mwuerms/rollin/sw/rollingL412/Core/Inc/main.h

#define USR_BTN_Pin LL_GPIO_PIN_13
#define USR_BTN_GPIO_Port GPIOC
#define DBG_TX_Pin LL_GPIO_PIN_2
#define DBG_TX_GPIO_Port GPIOA
#define DBG_RX_Pin LL_GPIO_PIN_3
#define DBG_RX_GPIO_Port GPIOA
#define SPI1_NSS_Pin LL_GPIO_PIN_4
#define SPI1_NSS_GPIO_Port GPIOA
#define USR_LED_Pin LL_GPIO_PIN_13
#define USR_LED_GPIO_Port GPIOB
#define NVIC_PRIORITYGROUP_0         ((uint32_t)0x00000007) /*!< 0 bit  for pre-emption priority,
#define NVIC_PRIORITYGROUP_1         ((uint32_t)0x00000006) /*!< 1 bit  for pre-emption priority,
#define NVIC_PRIORITYGROUP_2         ((uint32_t)0x00000005) /*!< 2 bits for pre-emption priority,
#define NVIC_PRIORITYGROUP_3         ((uint32_t)0x00000004) /*!< 3 bits for pre-emption priority,
#define NVIC_PRIORITYGROUP_4         ((uint32_t)0x00000003) /*!< 4 bits for pre-emption priority,
