mwuerms/rollin/sw/avrgcc/r1/pid.h

/**
 * Martin Egli
 * 2022-09-21
 *
 * pid controller module
 */

#ifndef _PID_H_
#define _PID_H_

// - include -------------------------------------------------------------------
#include <stdint.h>

// - public functions ----------------------------------------------------------

void pid_init(float kp, float ki, float kd);
float pid_exec(float error, float delta_t);

#endif // _PID_H_
