mwuerms/rollin/sw/rollin2/Core/Inc/project.h

/*
 * Martin Egli
 * 2025-07-02
 * project definitions and includes
 */

#ifndef INC_PROJECT_H_
#define INC_PROJECT_H_

#include <stdint.h>
#include <stdbool.h>
#include <stddef.h>
#include "main.h"

/* template to use later on
uint32_t primask;

primask = __get_PRIMASK();  // Save current interrupt state
__disable_irq();            // Disable all interrupts

// --- Critical Section Start ---
/ * Your critical code here * /
// --- Critical Section End ---

__set_PRIMASK(primask);     // Restore previous interrupt state
*/


#endif // INC_PROJECT_H_
