mwuerms/rollin/sw/avrgcc/r1/project.h

/**
 * Martin Egli
 * 2021-09-16
 *
 * basic project definitions
 */

#ifndef _PROJECT_H_
#define _PROJECT_H_
/* - includes --------------------------------------------------------------- */
#include <stdint.h>
#include "macrolib.h"

// - public definitions --------------------------------------------------------
#define RET_OK (0)
#define RET_ERR (1)

#define RET_AGAIN (RET_OK)
#define RET_STOP (RET_ERR)

/* - public variables ------------------------------------------------------- */
extern volatile uint8_t global_events;
#define EV_WAKEUP _BV(0)
#define EV_UPDATE_PWM _BV(1)
#define EV_READ_SENSOR _BV(2)

#define SEND_EVENT(ev) global_events |= ev

/* - functions -------------------------------------------------------------- */

#endif /* _PROJECT_H_ */
