mwuerms/rollin/sw/test1/Core/Src/main.c

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
/* Includes ------------------------------------------------------------------*/
#include "main.h"
#include "usb_device.h"

SPI_HandleTypeDef hspi1;

TIM_HandleTypeDef htim1;
TIM_HandleTypeDef htim2;

void SystemClock_Config(void);
static void MX_GPIO_Init(void);
static void MX_TIM1_Init(void);
static void MX_TIM2_Init(void);
static void MX_SPI1_Init(void);
/* USER CODE BEGIN 0 */
static volatile uint16_t sine_lookup_table[] = {32767, 37043, 41247, 45306, 49150, 52714, 55936, 58762, 61144, 63039, 64417, 65253, 65534, 65253, 64417, 63039, 61144, 58762, 55936, 52714, 49150, 45306, 41247, 37043, 32767, 28490, 24286, 20227, 16383, 12819, 9597, 6771, 4389, 2494, 1116, 280, 0, 280, 1116, 2494, 4389, 6771, 9597, 12819, 16383, 20227, 24286, 28490};
static const volatile uint16_t sine_lookup_table_size = sizeof(sine_lookup_table)/sizeof(sine_lookup_table[0]);
static volatile uint16_t pwm_A_index, pwm_B_index, pwm_C_index;
static uint16_t _inc(uint16_t x, uint16_t max) {
	if(x < max) {
		return x+1;
	}
	return 0;
}
void HAL_TIM_PWM_PulseFinishedCallback(TIM_HandleTypeDef *htim) {
	if(htim == &htim1) {
		HAL_GPIO_WritePin(GPIOA, GPIO_PIN_15, GPIO_PIN_SET);
		if(htim->Channel == HAL_TIM_ACTIVE_CHANNEL_1) {
			HAL_GPIO_WritePin(GPIOA, GPIO_PIN_15, GPIO_PIN_RESET);
			HAL_GPIO_WritePin(GPIOA, GPIO_PIN_15, GPIO_PIN_SET);
			pwm_A_index = _inc(pwm_A_index, sine_lookup_table_size-1);
			TIM1->CCR1 = sine_lookup_table[pwm_A_index];
		}
		if(htim->Channel == HAL_TIM_ACTIVE_CHANNEL_2) {
			HAL_GPIO_WritePin(GPIOA, GPIO_PIN_15, GPIO_PIN_RESET);
			HAL_GPIO_WritePin(GPIOA, GPIO_PIN_15, GPIO_PIN_SET);
			HAL_GPIO_WritePin(GPIOA, GPIO_PIN_15, GPIO_PIN_RESET);
			HAL_GPIO_WritePin(GPIOA, GPIO_PIN_15, GPIO_PIN_SET);
			pwm_B_index = _inc(pwm_B_index, sine_lookup_table_size-1);
			TIM1->CCR2 = sine_lookup_table[pwm_B_index];
		}
		if(htim->Channel == HAL_TIM_ACTIVE_CHANNEL_3) {
			HAL_GPIO_WritePin(GPIOA, GPIO_PIN_15, GPIO_PIN_RESET);
			HAL_GPIO_WritePin(GPIOA, GPIO_PIN_15, GPIO_PIN_SET);
			HAL_GPIO_WritePin(GPIOA, GPIO_PIN_15, GPIO_PIN_RESET);
			HAL_GPIO_WritePin(GPIOA, GPIO_PIN_15, GPIO_PIN_SET);
			HAL_GPIO_WritePin(GPIOA, GPIO_PIN_15, GPIO_PIN_RESET);
			HAL_GPIO_WritePin(GPIOA, GPIO_PIN_15, GPIO_PIN_SET);
			pwm_C_index = _inc(pwm_C_index, sine_lookup_table_size-1);
			TIM1->CCR3 = sine_lookup_table[pwm_C_index];
		}
		HAL_GPIO_WritePin(GPIOA, GPIO_PIN_15, GPIO_PIN_RESET);
	}
}

void HAL_GPIO_EXTI_Callback(uint16_t GPIO_Pin) {
	asm("NOP");
}

#define COM_BUFFER_SIZE	(256)
static struct {
	uint8_t data[COM_BUFFER_SIZE];
	uint16_t wr_idx;
} com_buffer;

void com_clear_buffer(void) {
	com_buffer.wr_idx = 0;
}

#include "usbd_cdc_if.h"
void com_send_buffer(void) {
	if(com_buffer.wr_idx == 0) {
		// nothing to send
		return;
	}
	if(CDC_Transmit_FS(com_buffer.data, com_buffer.wr_idx) == 0) {
		// OK
		asm("NOP");
	}
}


uint32_t com_append_char(char c) {
	if(com_buffer.wr_idx < (COM_BUFFER_SIZE-2)) {
		com_buffer.data[com_buffer.wr_idx++] = c;
		return 1;
	}
	return 0;
}

void com_append_string(char *str) {
	char c;
	// copy string
	while(1) {
		c = *str++;
		if(c == '\0') {
			// found end, do not copy
			break;
		}
		if(com_append_char(c) == 0) {
			// buffer full, stop
			break;
		}
	}
}

void com_append_int16(int16_t value) {
	uint16_t digit_pos, use_char;
	int16_t digits[] = {10000, 1000, 100, 10, 1};
	uint8_t digit_value;
	use_char = 0;
	// sign
	if(value < 0) {
		value *= -1;
		if(com_append_char('-') == 0) {
			// buffer full, stop
			return;
		}
	}
	if(value == 0) {
		// only append '0', and done here
		com_append_char('0');
		return;
	}
	for(digit_pos = 0; digit_pos < (sizeof(digits)/sizeof(digits[0])); digit_pos++) {
		digit_value = (uint8_t)(value/digits[digit_pos]);
		if((digit_value != 0) || (use_char != 0)) {
			use_char = 1;
			if(com_append_char('0'+digit_value) == 0) {
				// buffer full, stop
				return;
			}
			value -= digit_value * digits[digit_pos];
		}
	}
}

void com_append_int32(int32_t value) {
	uint16_t digit_pos, use_char;
	int32_t digits[] = {1000000000, 100000000, 10000000, 1000000, 100000, 10000, 1000, 100, 10, 1};
	uint8_t digit_value;
	use_char = 0;
	// sign
	if(value < 0) {
		value *= -1;
		if(com_append_char('-') == 0) {
			// buffer full, stop
			return;
		}
	}
	if(value == 0) {
		// only append '0', and done here
		com_append_char('0');
		return;
	}
	for(digit_pos = 0; digit_pos < (sizeof(digits)/sizeof(digits[0])); digit_pos++) {
		digit_value = (uint8_t)(value/digits[digit_pos]);
		if((digit_value != 0) || (use_char != 0)) {
			use_char = 1;
			if(com_append_char('0'+digit_value) == 0) {
				// buffer full, stop
				return;
			}
			value -= digit_value * digits[digit_pos];
		}
	}
}

void com_append_float(float f, uint32_t nb_dec_places) {
	int32_t x;

	x = (int32_t)f;
	com_append_int32(x);

	if(nb_dec_places == 0) {
		// do not add any decimal places
		return;

	}
	if(nb_dec_places >= 9) {
		// max is 9
		nb_dec_places = 9;
	}

	f -= (float)x;
	if(f < 0.0f) {
		f *= -1;
	}
	com_append_char('.');
	// eval nb leading '0' of part after '.'
	for(uint16_t n = 0; n < nb_dec_places; n++) {
		f *= 10;
		x = (uint8_t)f;
		f -= (float)x;
		com_append_char('0'+x);
	}
}

void _wait_some_time(void) {
		asm("NOP");
	for(uint32_t cnt = 100000; cnt; cnt--) {
	}
}

#define READ_CMD  (0x80)
#define WRITE_CMD (0x00)
void mpu9250_read_who_am_i(void) {
  uint8_t tx_data[1+1] = {READ_CMD|117};
  uint8_t rx_data[sizeof(tx_data)];
  HAL_GPIO_WritePin(SPI1_NSS_GPIO_Port, SPI1_NSS_Pin, GPIO_PIN_RESET);
  HAL_SPI_TransmitReceive(&hspi1, tx_data, rx_data, sizeof(tx_data), 10000);
  HAL_GPIO_WritePin(SPI1_NSS_GPIO_Port, SPI1_NSS_Pin, GPIO_PIN_SET);
}

void mpu9250_read_config(void) {
  uint8_t tx_data[1+7] = {READ_CMD|26};
  uint8_t rx_data[sizeof(tx_data)];
  HAL_GPIO_WritePin(SPI1_NSS_GPIO_Port, SPI1_NSS_Pin, GPIO_PIN_RESET);
  HAL_SPI_TransmitReceive(&hspi1, tx_data, rx_data, sizeof(tx_data), 10000);
  HAL_GPIO_WritePin(SPI1_NSS_GPIO_Port, SPI1_NSS_Pin, GPIO_PIN_SET);
}

void mpu9250_write_config(void) {
  uint8_t tx_data[] = {WRITE_CMD|26, 0x00, 0x00, (0x03<<2), 0x00, 0x00, 0x00};
  uint8_t rx_data[sizeof(tx_data)];
  HAL_GPIO_WritePin(SPI1_NSS_GPIO_Port, SPI1_NSS_Pin, GPIO_PIN_RESET);
  HAL_SPI_TransmitReceive(&hspi1, tx_data, rx_data, sizeof(tx_data), 10000);
  HAL_GPIO_WritePin(SPI1_NSS_GPIO_Port, SPI1_NSS_Pin, GPIO_PIN_SET);
}

void mpu9250_read_int_config(void) {
  uint8_t tx_data[1+4] = {READ_CMD|55};
  uint8_t rx_data[sizeof(tx_data)];
  HAL_GPIO_WritePin(SPI1_NSS_GPIO_Port, SPI1_NSS_Pin, GPIO_PIN_RESET);
  HAL_SPI_TransmitReceive(&hspi1, tx_data, rx_data, sizeof(tx_data), 10000);
  HAL_GPIO_WritePin(SPI1_NSS_GPIO_Port, SPI1_NSS_Pin, GPIO_PIN_SET);
}

void mpu9250_write_int_config(void) {
  uint8_t tx_data[] = {WRITE_CMD|55, 0xF0, 0x00, 0x00, 0x00};
  uint8_t rx_data[sizeof(tx_data)];
  HAL_GPIO_WritePin(SPI1_NSS_GPIO_Port, SPI1_NSS_Pin, GPIO_PIN_RESET);
  HAL_SPI_TransmitReceive(&hspi1, tx_data, rx_data, sizeof(tx_data), 10000);
  HAL_GPIO_WritePin(SPI1_NSS_GPIO_Port, SPI1_NSS_Pin, GPIO_PIN_SET);
}

uint16_t mpu9250_read_sensor_data(uint8_t *rx_data) {
  uint8_t tx_data[1+3*2+1*2+3*2] = {READ_CMD|59};
  //uint8_t rx_data[sizeof(tx_data)];
  HAL_GPIO_WritePin(SPI1_NSS_GPIO_Port, SPI1_NSS_Pin, GPIO_PIN_RESET);
  HAL_SPI_TransmitReceive(&hspi1, tx_data, rx_data, sizeof(tx_data), 10000);
  HAL_GPIO_WritePin(SPI1_NSS_GPIO_Port, SPI1_NSS_Pin, GPIO_PIN_SET);
  return sizeof(tx_data);
}

uint16_t mpu9250_read_acc_data(uint8_t *rx_data) {
  uint8_t tx_data[1+3*2] = {READ_CMD|59};
  //uint8_t rx_data[sizeof(tx_data)];
  HAL_GPIO_WritePin(SPI1_NSS_GPIO_Port, SPI1_NSS_Pin, GPIO_PIN_RESET);
  HAL_SPI_TransmitReceive(&hspi1, tx_data, rx_data, sizeof(tx_data), 10000);
  HAL_GPIO_WritePin(SPI1_NSS_GPIO_Port, SPI1_NSS_Pin, GPIO_PIN_SET);
  return sizeof(tx_data);
}

uint16_t mpu9250_read_temp_data(uint8_t *rx_data) {
  uint8_t tx_data[1+2] = {READ_CMD|65};
  //uint8_t rx_data[sizeof(tx_data)];
  HAL_GPIO_WritePin(SPI1_NSS_GPIO_Port, SPI1_NSS_Pin, GPIO_PIN_RESET);
  HAL_SPI_TransmitReceive(&hspi1, tx_data, rx_data, sizeof(tx_data), 10000);
  HAL_GPIO_WritePin(SPI1_NSS_GPIO_Port, SPI1_NSS_Pin, GPIO_PIN_SET);
  return sizeof(tx_data);
}

uint16_t mpu9250_read_gyro_data(uint8_t *rx_data) {
  uint8_t tx_data[1+3*2] = {READ_CMD|67};
  //uint8_t rx_data[sizeof(tx_data)];
  HAL_GPIO_WritePin(SPI1_NSS_GPIO_Port, SPI1_NSS_Pin, GPIO_PIN_RESET);
  HAL_SPI_TransmitReceive(&hspi1, tx_data, rx_data, sizeof(tx_data), 10000);
  HAL_GPIO_WritePin(SPI1_NSS_GPIO_Port, SPI1_NSS_Pin, GPIO_PIN_SET);
  return sizeof(tx_data);
}

/* MPU9250
1g = 16384 (2^14)
Accelerometer Umschlagsmessung Mittelwerte
2022-09-09, Martin Egli
angle	alpha	acc x	acc y	acc z
0	90	-116.95652173913	16533.1304347826	2896.86956521739
90	0	16381.9047619048	319.619047619048	2813.42857142857
180	-90	259	-16190.7777777778	2529.44444444444
270	-180	-16359.6470588235	-9.76470588235294	5139.17647058824

Gyro, Mittelwerte in Ruhe
gyro x	gyro y	gyro z
-249.254681220314	-99.6965046888321	-266.373261985954
 */
const float acc_1g = 16384.0f;
const float acc_meas_x_1g[] = {16381.9047619048f, -16359.6470588235f};
const float acc_meas_y_1g[] = {16533.1304347826f, -16190.7777777778f};
const float gyr_meas_z_0 = -266.373261985954f;

typedef struct {
	float gain, offset;
} gain_offset_t;

struct {
	gain_offset_t x;
	gain_offset_t y;
} mpu9250_corr_acc;
float acc_xy_angle_deg_corr = -90.0f;

float mpu9250_calc_acc(int16_t value, gain_offset_t *corr) {
	return corr->gain * (float)value + corr->offset;
}
#include <math.h>
float acc_to_alpha_rad(float x, float y) {
	return atan2((double)x, (double)y);
}
float rad_to_deg(float a_rad) {
	return a_rad * 180.0f / M_PI;
}

struct {
	float x, y;
} acc_values;
float acc_xy_angle_deg;
float gyr_z_angle_deg;
float angle_deg, angle_deg_prev;


#define SEP_SERIAL_PLOTTER ' ' // better serial plotter uses ' ' (space)
#define SEP SEP_SERIAL_PLOTTER
/* USER CODE END 0 */

/**
  * @brief  The application entry point.
  * @retval int
  */
int main(void)
{
  /* USER CODE BEGIN 1 */
	// calc correction values for acc_x, acc_y
	mpu9250_corr_acc.x.gain    = (2*acc_1g)/(acc_meas_x_1g[0] - acc_meas_x_1g[1]); // a = dy/dx
	mpu9250_corr_acc.x.offset = acc_1g - mpu9250_corr_acc.x.gain*acc_meas_x_1g[0]; // b = y0 - a*x0

	mpu9250_corr_acc.y.gain    = (2*acc_1g)/(acc_meas_y_1g[0] - acc_meas_y_1g[1]); // a = dy/dx
	mpu9250_corr_acc.y.offset = acc_1g - mpu9250_corr_acc.y.gain*acc_meas_y_1g[0]; // b = y0 - a*x0

  /* USER CODE END 1 */

  /* MCU Configuration--------------------------------------------------------*/

  /* Reset of all peripherals, Initializes the Flash interface and the Systick. */
  HAL_Init();

  /* Configure the system clock */
  SystemClock_Config();

  /* Initialize all configured peripherals */
  MX_GPIO_Init();
  MX_TIM1_Init();
  MX_TIM2_Init();
  MX_USB_DEVICE_Init();
  MX_SPI1_Init();
  /* USER CODE BEGIN 2 */


  mpu9250_read_who_am_i();
  mpu9250_read_config();
  mpu9250_write_config();
  mpu9250_read_int_config();


  asm("NOP");
  /* USER CODE END 2 */

  /* Infinite loop */
  /* USER CODE BEGIN WHILE */
  uint8_t sensor_data[32];
  int16_t value;
  com_clear_buffer();
  com_append_string("acc x, acc y, acc z, gyro x, gyro y, gyro z, temp\n");
  com_send_buffer();
  angle_deg_prev = 0.0f;
  while (1)
  {
    /* USER CODE END WHILE */

    /* USER CODE BEGIN 3 */
	  com_clear_buffer();
	  mpu9250_read_sensor_data(sensor_data);
	  // acc
	  value = (int16_t)((sensor_data[1] << 8) + sensor_data[2]); // acc x
	  acc_values.x = mpu9250_calc_acc(value, &mpu9250_corr_acc.x);
	  //com_append_int16(value);
	  //com_append_char(',');
	  value = (int16_t)((sensor_data[3] << 8) + sensor_data[4]); // acc y
	  acc_values.y = mpu9250_calc_acc(value, &mpu9250_corr_acc.y);
	  //com_append_int16(value);
	  //com_append_char(SEP);
	  value = (int16_t)((sensor_data[5] << 8) + sensor_data[6]); // acc z
	  //com_append_int16(value);
	  //com_append_char(SEP);

	  // gyro
	  value = (int16_t)((sensor_data[9] << 8) + sensor_data[10]); // gyro x
	  //com_append_int16(value);
	  //com_append_char(SEP);
	  value = (int16_t)((sensor_data[11] << 8) + sensor_data[12]); // gyro y
	  //com_append_int16(value);
	  //com_append_char(SEP);
	  value = (int16_t)((sensor_data[13] << 8) + sensor_data[14]); // gyro z
	  //com_append_int16(value);
	  //com_append_char(SEP);

	  //float gyr_sample_rate = 0.260; // 260 ms
	  //float gyr_z_rate_deg;

	  gyr_z_angle_deg = (float)value; // RATE! in deg/s -> * s -> deg
	  gyr_z_angle_deg -= gyr_meas_z_0;
	  gyr_z_angle_deg *= (250.0f/32768.0f); // scale to +/-250 dps
	  gyr_z_angle_deg = gyr_z_angle_deg * 0.02685f;
	  com_append_float(gyr_z_angle_deg, 5);
	  com_append_char(SEP);


	  //com_append_float(acc_values.x, 5);
	  //com_append_char(SEP);

	  //com_append_float(acc_values.y, 5);
	  //com_append_char(SEP);


		acc_xy_angle_deg = acc_to_alpha_rad(acc_values.x, acc_values.y);
		acc_xy_angle_deg = rad_to_deg(acc_xy_angle_deg);
		acc_xy_angle_deg += acc_xy_angle_deg_corr;

		com_append_float(acc_xy_angle_deg, 5);
		com_append_char(SEP);

		// dragon bot
		//angle_deg = 0.9934f * (angle_deg_prev + gyr_z_angle_deg) + 0.0066f * acc_xy_angle_deg;

		angle_deg = 0.95f * (angle_deg_prev + gyr_z_angle_deg) + 0.05f * acc_xy_angle_deg;

		com_append_float(angle_deg, 5);
		com_append_char(SEP);

		angle_deg_prev = angle_deg;

	  // temp
	  value = (int16_t)((sensor_data[7] << 8) + sensor_data[8]); // temp
	  com_append_int16(value);
	  com_append_char('\n');

	  com_send_buffer();
	  _wait_some_time();
  }
  /* USER CODE END 3 */
}

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
